besi/bathtub-boat/sw/secrets.example.py

class wifi:
   aps = {
       'SSID1': 'PASSWORD1',
       'SSID2': 'PASSWORD2',       
       }

class mqtt:
    host = 'mqtt://yourserver.com'
    topic = 'your.topic'
    user = 'john'
    password = 'secret'
    port = 1883
